svpetry/TeslaBMBCheck/MCU/TeslaBMBCheck.X/bms.h

/* 
 * File:   bms.h
 * Author: svpet
 *
 * Created on June 14, 2025, 7:50 AM
 */

#ifndef BMS_H
#define	BMS_H

#include "types.h"

#define CELL_COUNT 6

uint8_t FindBoardId(void);
bool ResetBoard(void);
bool SetNewBoardId(uint8_t id);
struct BmsData ReadBmsData(uint8_t module_id);
void EnableBmsBalancers(uint8_t module_id, uint8_t balancer_bits);
void ClearBmsFaults(uint8_t module_id);

#endif	/* BMS_H */
